skndungu/relay_logic_firmware/hardware/img/relay_logic_board_6.png

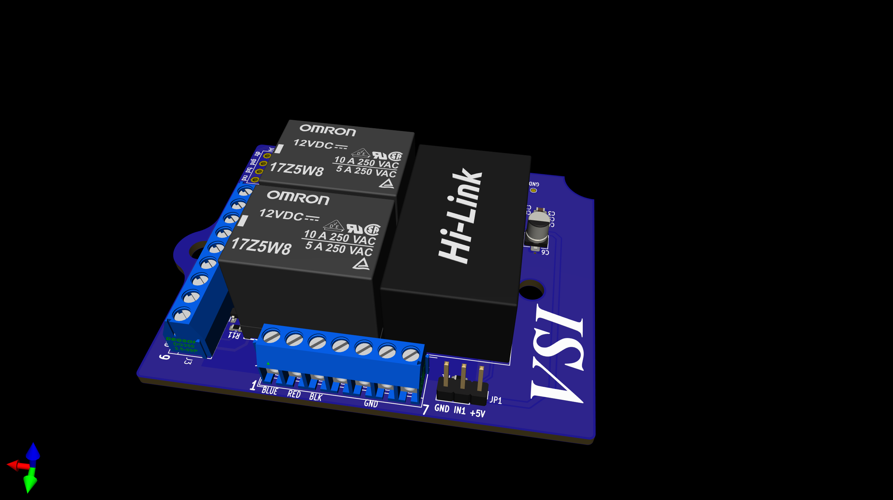
hardware/img/relay_logic_board_6.png
