skndungu/relay_logic_firmware/hardware/img/relay_logic_board_7.png

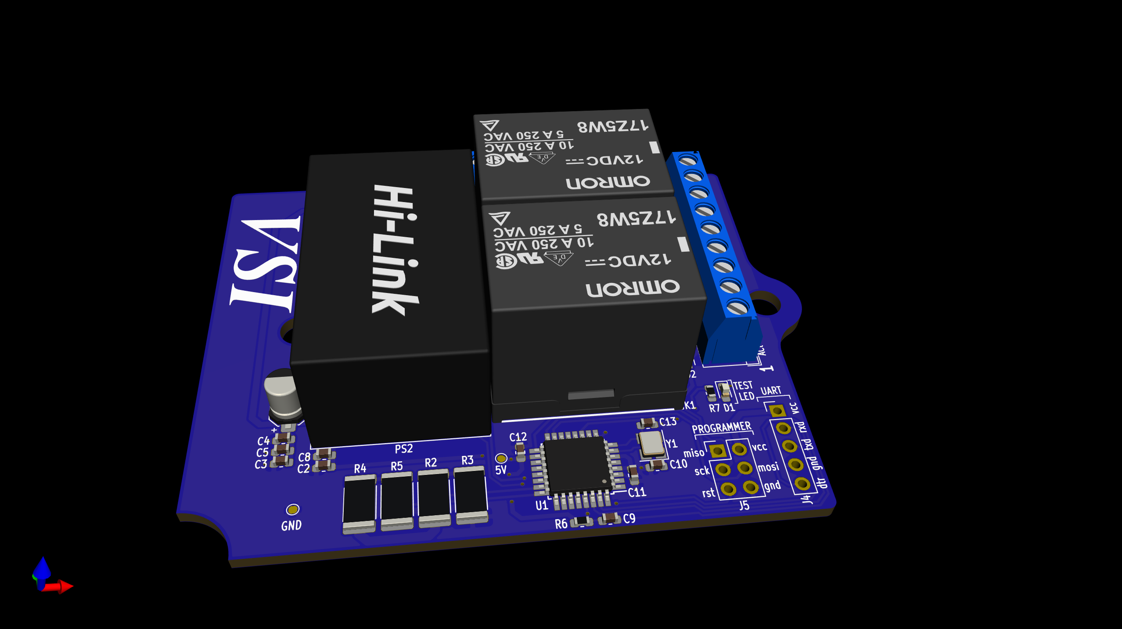
hardware/img/relay_logic_board_7.png
